uncle-ben-devel/hskanner3d/design/towers_scanner_cad/array_preview.PNG

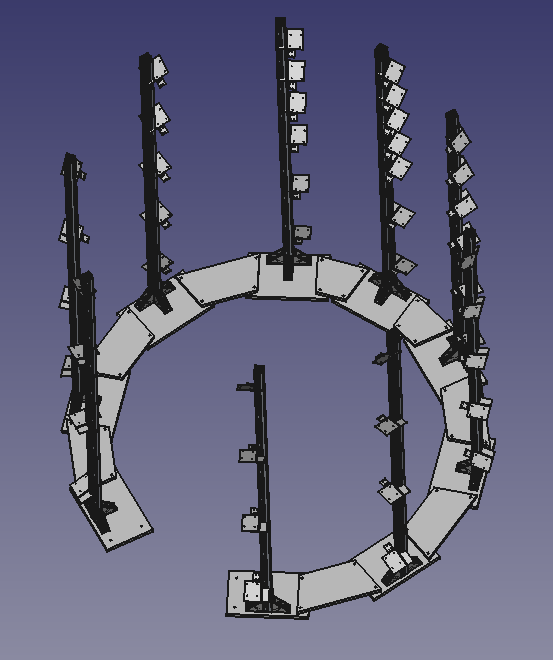
design/towers_scanner_cad/array_preview.PNG
