uncle-ben-devel/hskanner3d/design/towers_scanner_cad/baseplate-holes.png

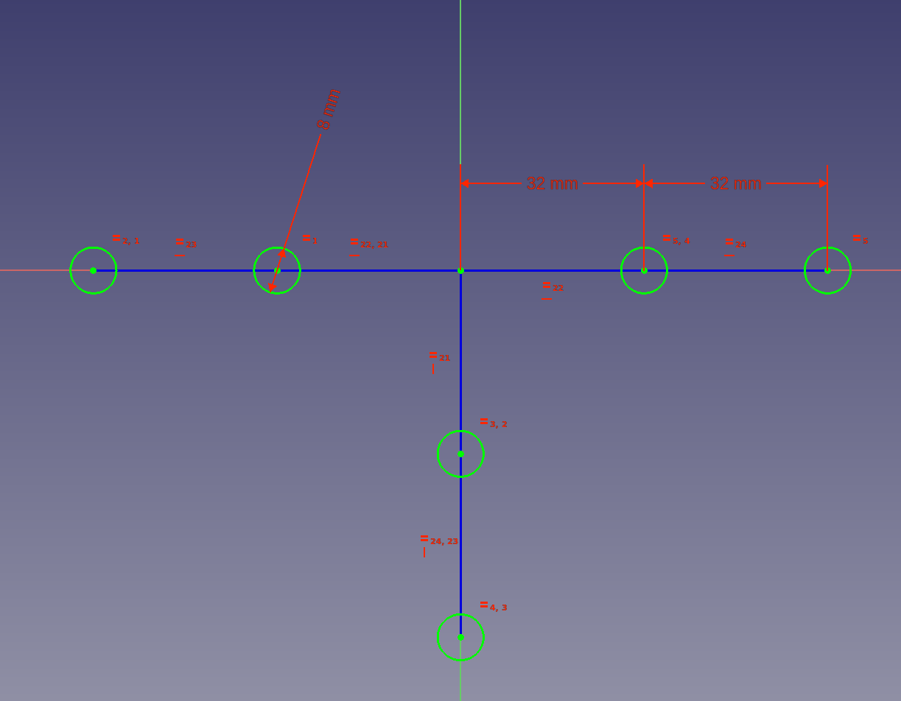
design/towers_scanner_cad/baseplate-holes.png
