uncle-ben-devel/hskanner3d/design/position_estimation/CCTAGmarkersToPrint/00022-1.png

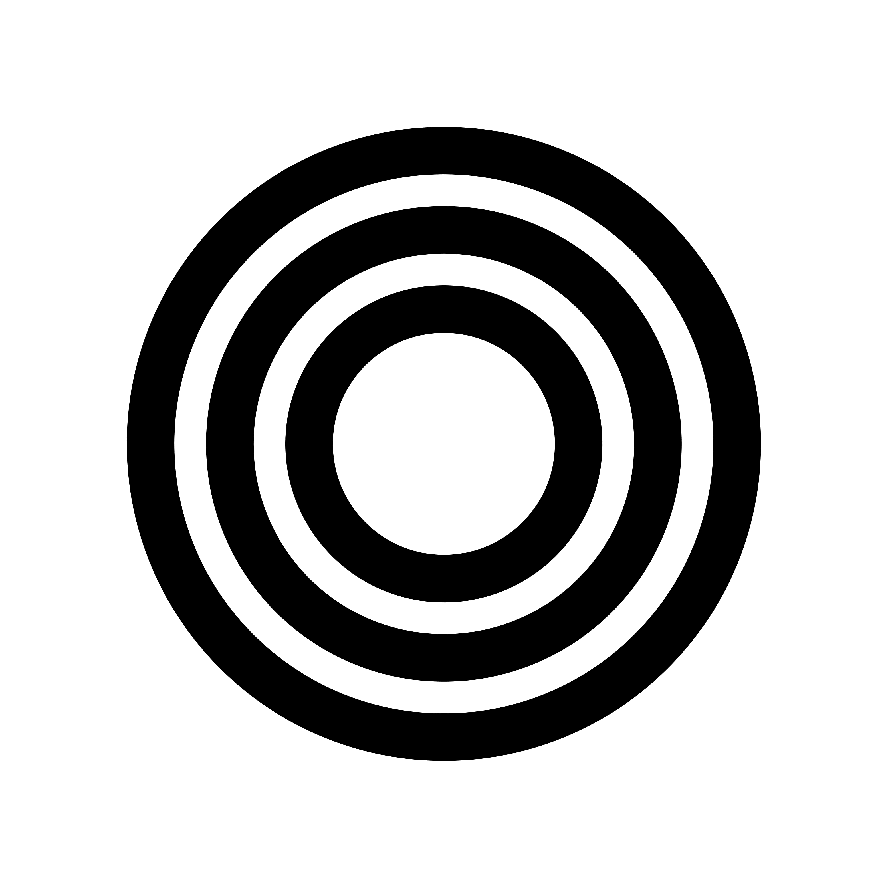
design/position_estimation/CCTAGmarkersToPrint/00022-1.png
