uncle-ben-devel/hskanner3d/design/position_estimation/CCTAGmarkersToPrint/00029-1.png

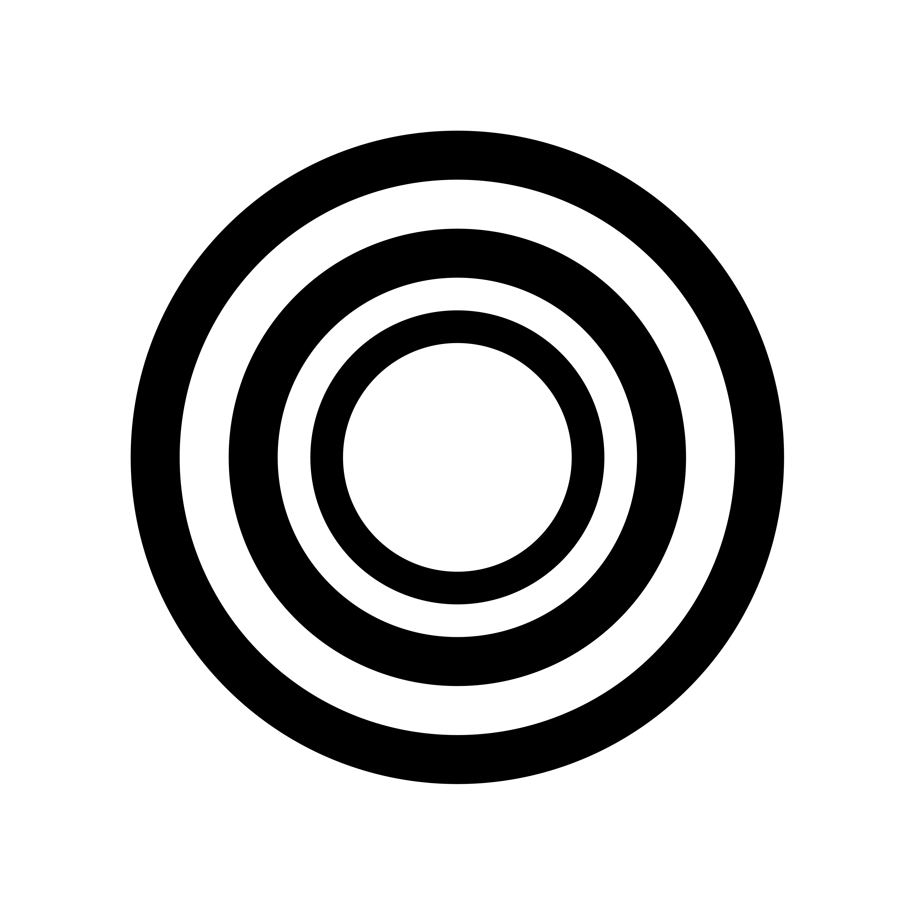
design/position_estimation/CCTAGmarkersToPrint/00029-1.png
